autowattage/2swap/tvhead/software/images/expressions/angry.png

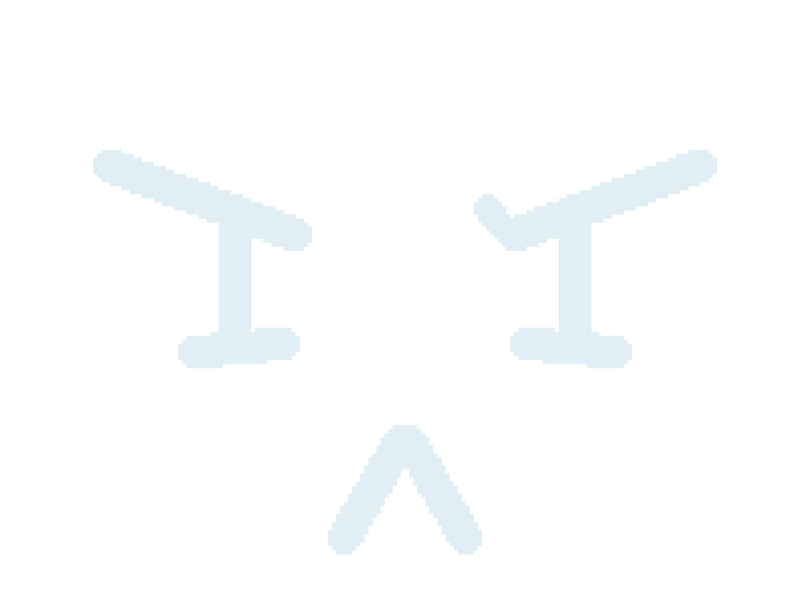
tvhead/software/images/expressions/angry.png
