autowattage/2swap/tvhead/software/images/expressions/excited.png

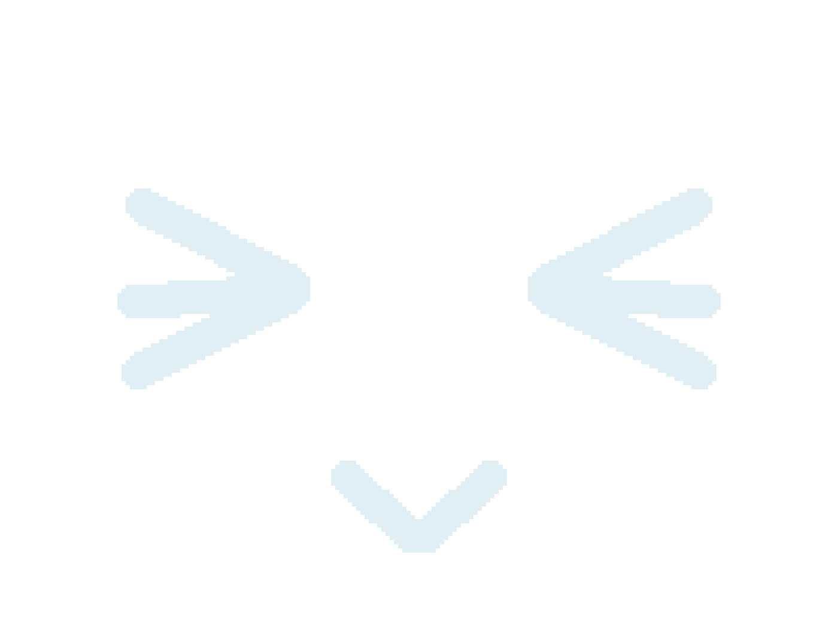
tvhead/software/images/expressions/excited.png
