autowattage/2swap/tvhead/software/images/expressions/head.png

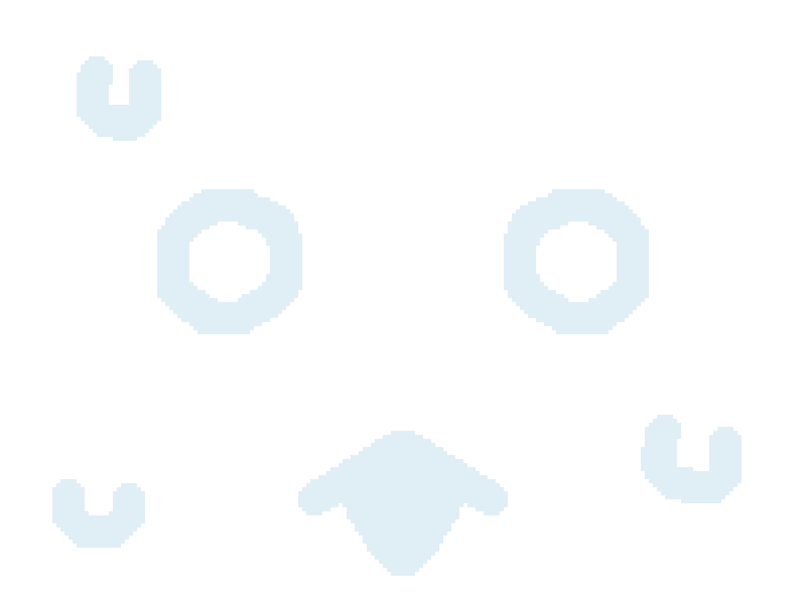
tvhead/software/images/expressions/head.png
