autowattage/2swap/tvhead/software/images/expressions/relaxed.png

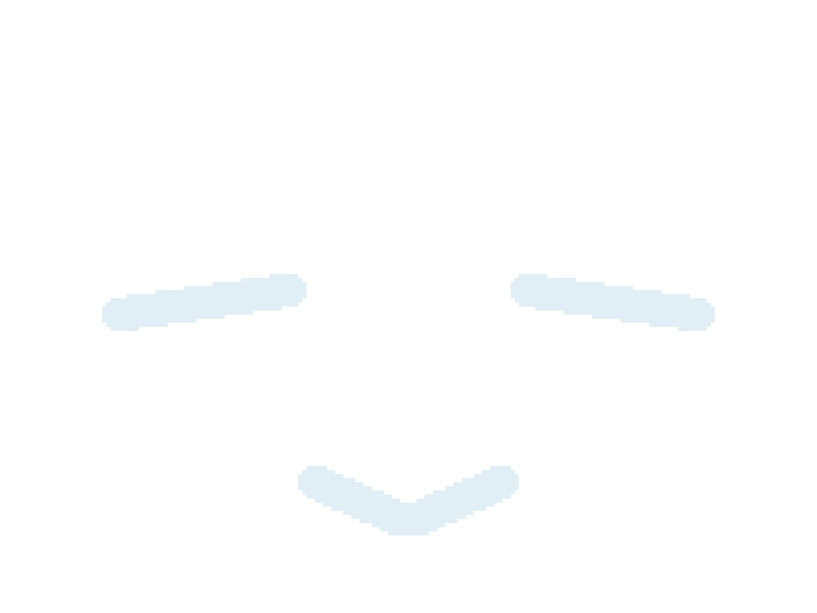
tvhead/software/images/expressions/relaxed.png
