autowattage/2swap/tvhead/software/images/expressions/sad.png

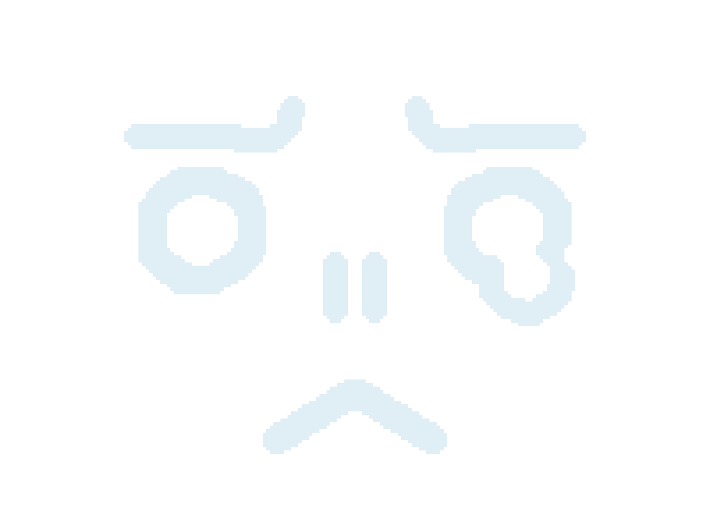
tvhead/software/images/expressions/sad.png
