autowattage/2swap/tvhead/software/images/expressions/surprised.png

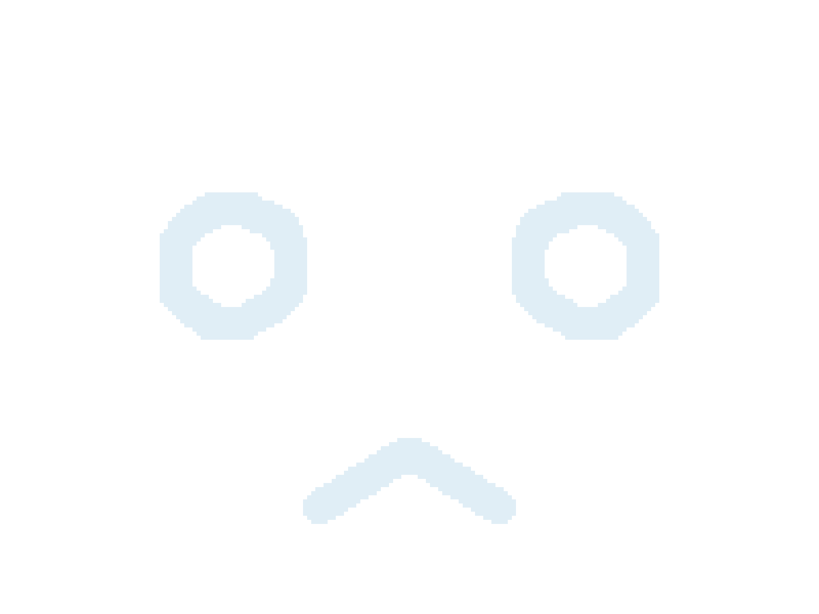
tvhead/software/images/expressions/surprised.png
