autowattage/2swap/tvhead/software/images/eyes/blink1.png

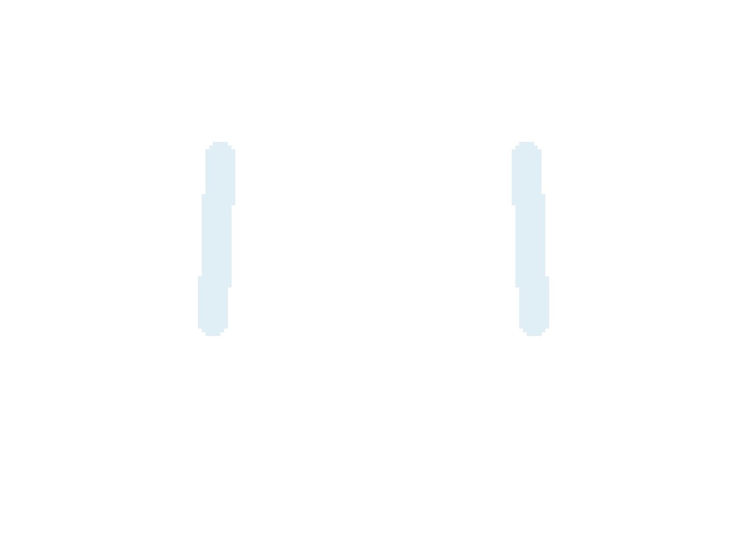
tvhead/software/images/eyes/blink1.png
