autowattage/2swap/tvhead/software/images/mouth/idle.png

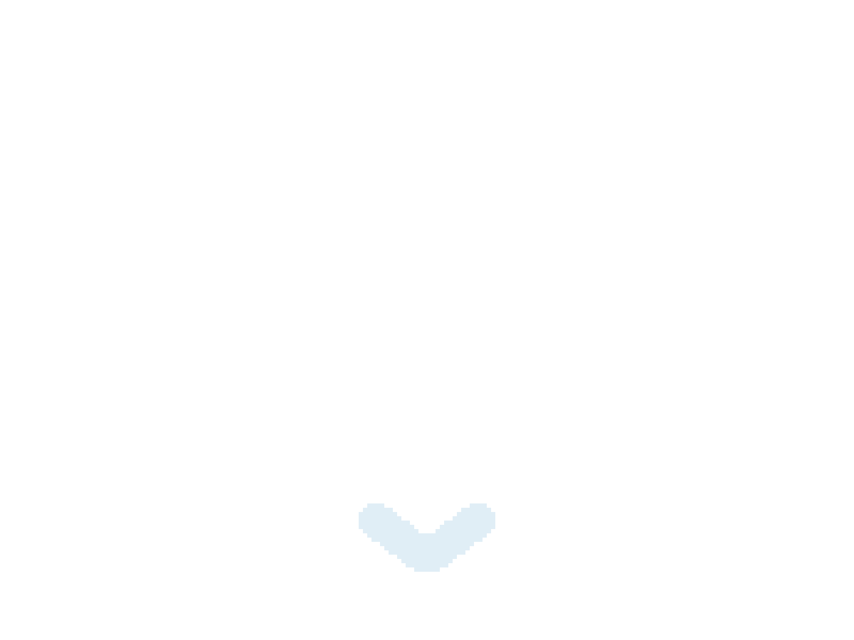
tvhead/software/images/mouth/idle.png
